andykarpov/karabas-go/case/xdemox_with_fdd/with logo/big logo/Karabas_Go_wd_logo_-_case_top_v1.0.stl

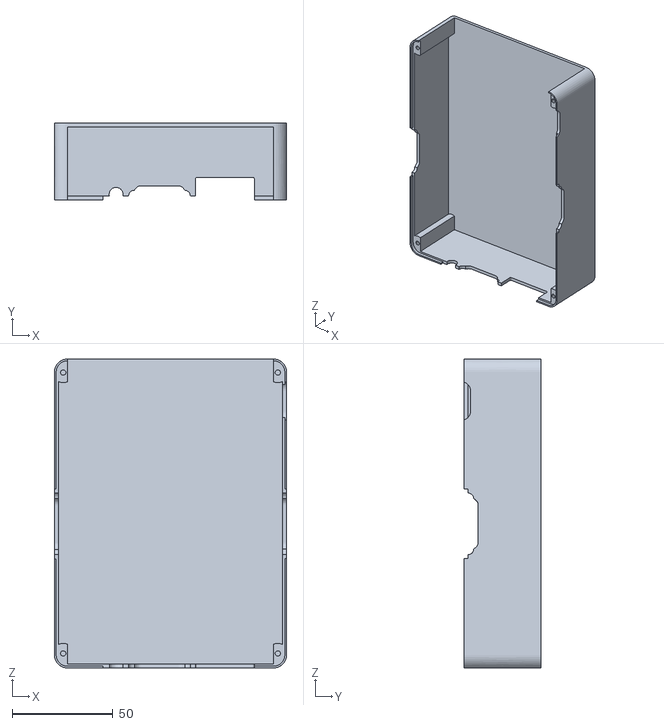
[picture p16: CAD file, 2024-03-02]
case/xdemox_with_fdd/with logo/big logo/Karabas_Go_wd_logo_-_case_top_v1.0.stl
115.3 x 38.0 x 153.3
