andykarpov/karabas-go/case/gotek_b4/front.stl

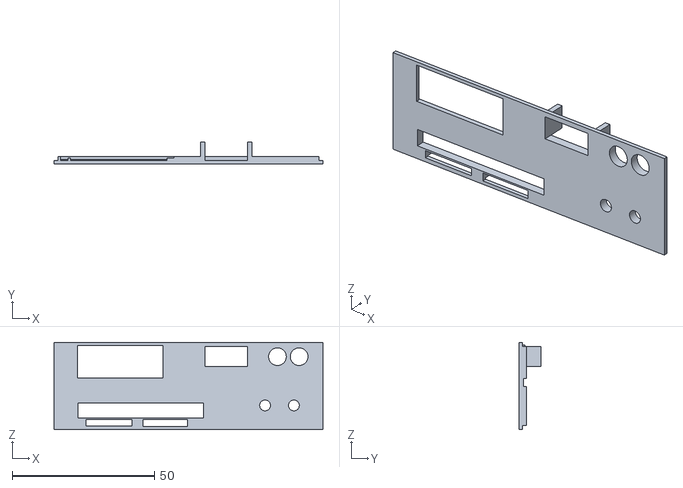
[picture p17: CAD file, 2026-05-31]
case/gotek_b4/front.stl
94.5 x 7.60 x 30.6
