andykarpov/karabas-go/case/gotek_b4/top.stl

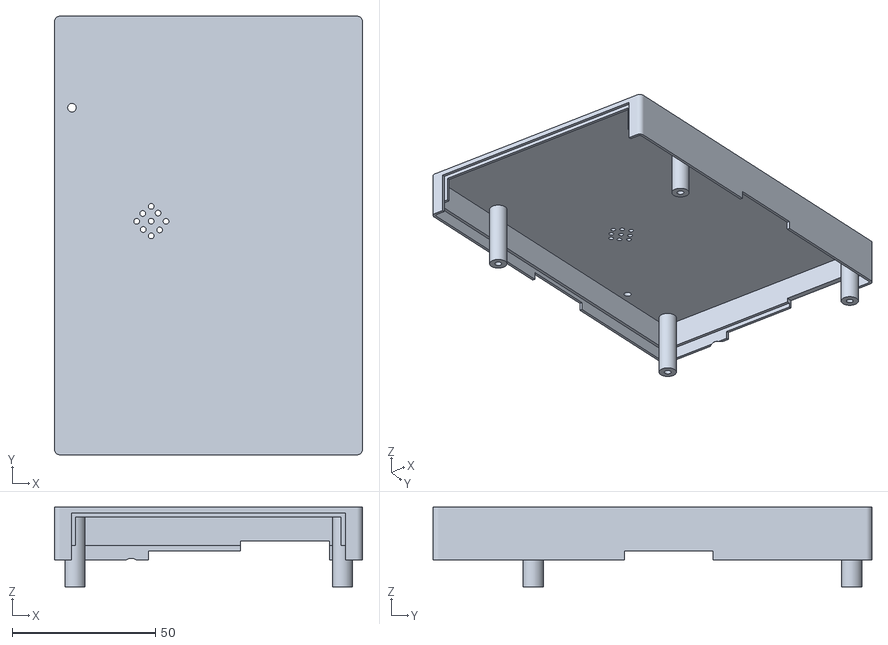
[picture p18: CAD file, 2026-05-31]
case/gotek_b4/top.stl
107.6 x 153.3 x 27.9
