andykarpov/karabas-go/case/gotek_b4/gotek.stl

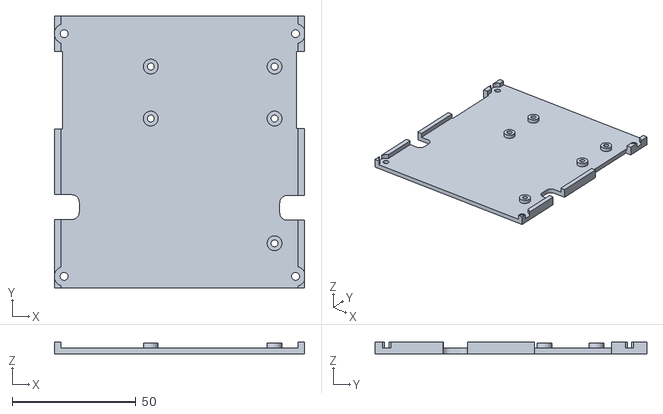
[picture p19: CAD file, 2026-05-31]
case/gotek_b4/gotek.stl
101.0 x 109.8 x 4.80
